ViniciusFranklin22/Automated-Irrigation-System-ESP32-MQTT-Flask-/server_get_msg.py

import pandas as pd
import paho.mqtt.client as mqtt
import json
import os
import threading

TOPIC_RECEIVE = "esp32-001/send"
csv_path = 'C:\\Users\\vinic\\Documents\\Projetos_ESP32\\Laboratório de Projetos Eletrônicos\\Testes MQTT\\MQTT\\data.csv'

BROKER = ""
PORT = 1883

# 🔒 lock para evitar escrita simultânea
lock = threading.Lock()

def on_connect(client, userdata, flags, rc):
    if rc == 0:
        print("✅ Conectado ao broker MQTT!")
        client.subscribe(TOPIC_RECEIVE, qos=1)
        print(f"📥 Inscrito no tópico: {TOPIC_RECEIVE}")
    else:
        print(f"❌ Falha na conexão. Código de erro: {rc}")

def on_message(client, userdata, msg):
    try:
        payload = msg.payload.decode('utf-8')
        data = json.loads(payload)

        if not isinstance(data, dict):
            print("⚠️ Payload inválido")
            return

        df = pd.DataFrame([data])

        # 🔥 escrita segura com lock
        with lock:
            df.to_csv(
                csv_path,
                mode='a',  # append
                header=not os.path.exists(csv_path),
                index=False
            )

        print(f"✅ Dados salvos: {data}")

    except Exception as e:
        print(f"⚠️ Erro ao processar mensagem: {e}")

client = mqtt.Client()

client.on_connect = on_connect
client.on_message = on_message

print("🔌 Conectando ao broker...")
client.connect(BROKER, PORT, keepalive=60)

client.loop_forever()
